asadmaza/Smart-Parking-System-IoT-Project/7. 3D models (Print)/ultrasonic-sensor-housing-hc-sr04-1.snapshot.1/PShop-Ultrasonico-1.png

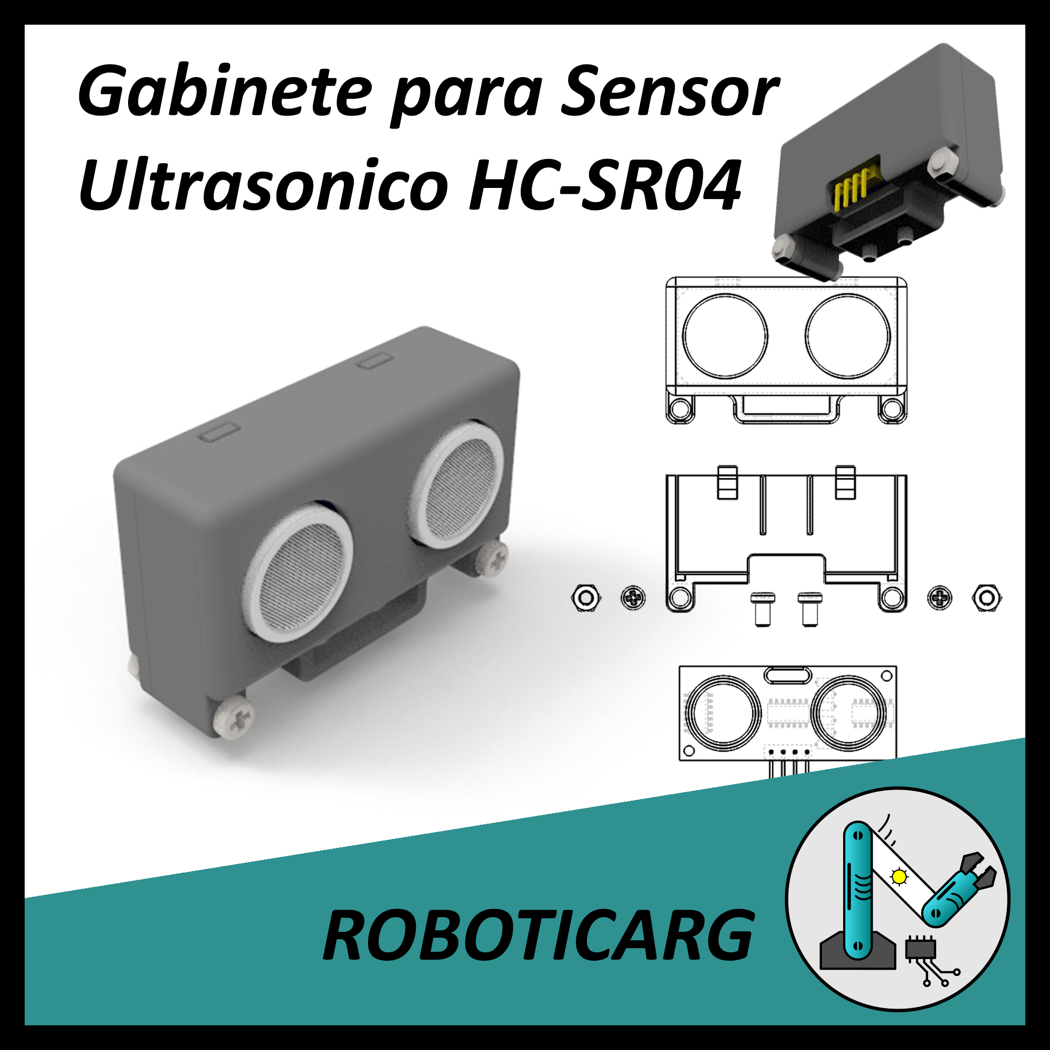
7. 3D models (Print)/ultrasonic-sensor-housing-hc-sr04-1.snapshot.1/PShop-Ultrasonico-1.png
