asadmaza/Smart-Parking-System-IoT-Project/8. RPI Local Script/Multimodal test AND real calibrated.py

"""

Threshold values are calibrated for Toy cars in this file, using trial
and error.

Threshold values:
Sensor                  |   Variable name
Ultrasonic sensor       |   threshold_max = 200.0 # in cm
Magnetometer sensor     |   sensor_threshold = 0.01 # in percent 
Magnetometer sensor     |   base_val_threshold = 0.008 # in percent



Multimodal Sensor AND testing file to measure the accuracy and the
detection of a car in the bay.

This is an AND test - if both sensors detect a car in the bay,
the LED will turn from Green (free) to Red (occupied)

Components required:
x1 Raspberry Pi Kit (RPI, cables, power source, breadboard etc.)
x1 5mm Red LED GPIO 
x1 5mm Green LED
x2 330 ohm resistors
x1 Ultrasonic Sensor
x1 Magnetometer

Code description:
File to test the ultrasonic sensor measurement accuracy, prints out
value when the code is run:
- Distance measured when bay is occupied
- Distance measured when bay is free
- % Accuracy with actual (ground truth) measured using measuring
tape or micrometer.
--------------------------------------------------------------------
Setup:
Will need to create a circuit diagram for the connection of
ultrasonic sensor and 2 LEDs.

Ensure the Ultrasonic sensor is connected as described:
• VCC connects to Pin 2 (5V)
• Trig connects to GPIO Pin 8
• Echo connects to R1 (1k OHM)
• R2 and R3 (1k OHM + 1 k OHM) connects from R1 to Ground
• Wire from R1 and R2+R3 connects to GPIO Pin 7
• GND connects to Pin 34 (Ground)

LED(GPIO 5) - Green LED
LED(GPIO 6) - Red LED

Magnetometer:
Needs I2C communication enabled on RPI
SDA to GPIO 2/SDA (in I2C Data mode enabled)
SCL to GPIO 3/SCL (in I2C Data mode enabled)
3.3V to 3V Pin
GND to GND pin

--------------------------------------------------------------------

Date: 10/10/2023
Author: Asad Maza - Group 3
"""
# Imports
import RPi.GPIO as GPIO
import time
import json
from AWSIoTPythonSDK.MQTTLib import AWSIoTMQTTClient
import os
from gpio_reset import all_pins_to_off
from PiicoDev_QMC6310 import PiicoDev_QMC6310
from PiicoDev_Unified import sleep_ms


# Define distance measuring function
def read_distance(TRIG, ECHO):
    GPIO.output(TRIG, False)
    time.sleep(1.5) # changed sleep time to read faster.
    GPIO.output(TRIG, True)
    time.sleep(0.00001)
    GPIO.output(TRIG, False)    
    while GPIO.input(ECHO)==0:
        pulse_start = time.time()
    while GPIO.input(ECHO)==1:
        pulse_end = time.time()
    pulse_duration = pulse_end - pulse_start
    distance = (pulse_duration * 34300) / 2
    distance = round(distance, 2)
    return distance

# GPIO config
GPIO.setmode(GPIO.BCM)
GPIO.setwarnings(False)
GPIO.setup(5, GPIO.OUT)
GPIO.setup(6, GPIO.OUT)
GPIO.setup(8, GPIO.OUT)
GPIO.setup(7, GPIO.IN)
green_LED = GPIO.output(5, GPIO.HIGH)
red_LED = GPIO.output(6, GPIO.LOW)


# Topic Constant
BAY_STATUS_CHANGE_FROM_DEVICE = "BAY_STATUS_CHANGE_FROM_DEVICE" # publish to this
SEND_BAY_CHANGE_STATUS_WHEN_RESERVED = "SEND_BAY_CHANGE_STATUS_WHEN_RESERVED" # subscribe to this
SEND_BAY_CHANGE_STATUS_WHEN_RESERVATION_EXPIRED = "SEND_BAY_CHANGE_STATUS_WHEN_RESERVATION_EXPIRED" # subscribe to this

# AWS IoT client setup
myMQTTClient = AWSIoTMQTTClient("testCertif")
myMQTTClient.configureEndpoint("a30y98prchbi0n-ats.iot.us-west-2.amazonaws.com", 8883)
myMQTTClient.configureCredentials(os.path.abspath(os.getcwd())+"/testCertif/root-CA.crt",
                                      os.path.abspath(os.getcwd())+"/testCertif/testCertif.private.key",
                                      os.path.abspath(os.getcwd())+"/testCertif/testCertif.cert.pem")

# Confirm MQTT Connection
myMQTTClient.connect()


# LED, sensor, state and type mapping for each bay
bay_mapping = {
    'A1': {'red_led': 6, 'yellow_or_green_led': 5, 'sensor_trigger': 8, 'sensor_echo': 7, 'state': 0, 'prev_state': 0, 'bay_type': 1, 'is_bay_booked' : 0}
}

# Initialise interval variables for publish and check bay status
publish_bay_mapping_interval = 10  # Publish every 10 seconds
check_bay_status_interval = 0.5  # Queries bay status every (1 + 0.5) seconds

last_publish_time = time.time()
last_check_time = time.time()

last_publish_time = 0
last_check_time = time.time()


def customCallback(client, userdata, message):
    if(message.topic == SEND_BAY_CHANGE_STATUS_WHEN_RESERVED):
        print("Received a reservation from flask : ")
        getAReservationFromFlask(message.payload.decode("utf-8"))
    elif(message.topic == SEND_BAY_CHANGE_STATUS_WHEN_RESERVATION_EXPIRED):
        print("Received a reservation expiry from flask : ")
        getAReservationExpiryFromFlask(message.payload.decode("utf-8"))

myMQTTClient.subscribe(SEND_BAY_CHANGE_STATUS_WHEN_RESERVED, 1, customCallback)
myMQTTClient.subscribe(SEND_BAY_CHANGE_STATUS_WHEN_RESERVATION_EXPIRED, 1, customCallback)

def getDataFromJsonString(jsonString):
    commaSplit = jsonString.split(',')
    onlyData = commaSplit[1].replace('{', '')
    onlyData = onlyData.replace('}', '')
    onlyData = onlyData.split(':')
    parkingName = onlyData[1].replace('"','').strip()
    return parkingName

def getAReservationFromFlask(messagePayload):
    json_object = json.loads(messagePayload)
    parkingName = getDataFromJsonString(json_object)
    global available_bays
    available_bays -= 1
    bay_mapping[parkingName]["is_bay_booked"] = 1
    GPIO.output(info['yellow_or_green_led'], False)
    GPIO.output(info['red_led'], True)

def getAReservationExpiryFromFlask(messagePayload):
    json_object = json.loads(messagePayload)
    parkingName = getDataFromJsonString(json_object)
    global available_bays
    available_bays += 1
    bay_mapping[parkingName]["is_bay_booked"] = 0
    GPIO.output(info['yellow_or_green_led'], True)
    GPIO.output(info['red_led'], False)




threshold_max = 20.0 # in cm
threshold_min = 0.0 # in cm

# initalise continue_loop to Yes
continue_loop = "Yes"

# Initialise threshold value
sensor_threshold = 0.015 # in percent (e.g. 10% = 0.10)

base_val_threshold = 0.005 # in percent (e.g. 2% = 0.02)
# Initialise sensor
magSensor = PiicoDev_QMC6310(range=3000)
def get_average(data_list):
    return sum(data_list) / len(data_list)

def collect_data_for_seconds(seconds):
    data_list = []
    for _ in range(seconds):
        raw_data = magSensor.read()
        z_axis_strength = raw_data['z']
        data_list.append(z_axis_strength)
        sleep_ms(1000)
    return data_list

print("Ultrasonic and Magnetometer sensor mounted at top of bay")
print("Formula for change_in_magnetfic_flux_density: abs((z_axis_strength - default_value) / default_value) * 100%")

# Loop until a valid default value is obtained
while True:
    # Read the data of the previous ten seconds
    data_list = collect_data_for_seconds(10)
    
    # If the data fluctuation is less than 2%, set it as the default value
    avg_value = get_average(data_list)
    max_value = max(data_list)
    min_value = min(data_list)
    fluctuation = (max_value - min_value) / avg_value
    
    if fluctuation < base_val_threshold:
        default_value = avg_value
        break


try:
    initial_publish = True # Flag to force initial publish
    state_changed = False  # Flag to indicate whether state has changed
    
    while continue_loop == "Yes":
        current_time = time.time()
        raw_data = magSensor.read()
        z_axis_strength = raw_data['z']
        print("observation value : "+ str(default_value))
        print("change in magnetic flux density : ", abs((z_axis_strength - default_value) / default_value)*100)

        # Check status of each bay if enough time has elapsed since the last check
        if current_time - last_check_time >= check_bay_status_interval:
            last_check_time = current_time
            
            timestamp = time.strftime("%Y-%m-%d %H:%M:%S")
            
            for bay, info in bay_mapping.items():
                dist_measured = read_distance(info['sensor_trigger'], info['sensor_echo'])
                # Remember previous state
                info['prev_state'] = info['state']
                
                # Check toy car presence based on Ultrasonic sensor distance measurement and Magnetometer conditional
                if (dist_measured <= threshold_max and dist_measured >= threshold_min) and (abs((z_axis_strength - default_value) / default_value) > sensor_threshold):
                    print("magnetometer difference :"+ str((z_axis_strength - default_value) / default_value))
                    print("Z-axis strength:", z_axis_strength)
                    print("detected car")
                    print("")
                    print(f"{bay} Distance: {dist_measured} Bay State: {info['state']}")
                    print("magnetometer and ultrasonic are detecting something and bay status is occupied")
                    if info['state'] == 0:
                        info['state'] = 1
                        state_changed = True  # State has changed
                        green_LED = GPIO.output(5, GPIO.LOW)
                        red_LED = GPIO.output(6, GPIO.HIGH)
                        bayStatus = {"state":info['state']}
                        result = {
                            bay : bayStatus
                        }
                        message = json.dumps({"timestamp": timestamp, "data": result})
                        try:
                            myMQTTClient.publish(BAY_STATUS_CHANGE_FROM_DEVICE, message, 1)
                        except Exception as e:
                            print(f"An exception occurred while publishing: {e}")
              
                        
                else:
                    print("magnetometer difference :"+ str((z_axis_strength - default_value) / default_value))
                    print("Z-axis strength:", z_axis_strength)
                    print("no car")
                    print("")
                    print(f"{bay} Distance: {dist_measured} Bay State: {info['state']}")
                    print("magnetometer and/or ultrasonic are not detecting something and bay status is free")
                    if info['state'] == 1:
                        info['state'] = 0
                        state_changed = True  # State has changed
                        green_LED = GPIO.output(5, GPIO.HIGH)
                        red_LED = GPIO.output(6, GPIO.LOW)
                        bayStatus = {"state":info['state']}
                        result = {
                            bay : bayStatus
                        }
                        message = json.dumps({"timestamp": timestamp, "data": result})
                        try:
                            myMQTTClient.publish(BAY_STATUS_CHANGE_FROM_DEVICE, message, 1)
                        except Exception as e:
                            print(f"An exception occurred while publishing: {e}")                        
                        
                        
                
                
                print("-" * 50)
                
                
except KeyboardInterrupt:
    print("Terminating and cleaning up")
    all_pins_to_off()
